raspberrypilearning/grandpa-scarer/en/images/gpio.png

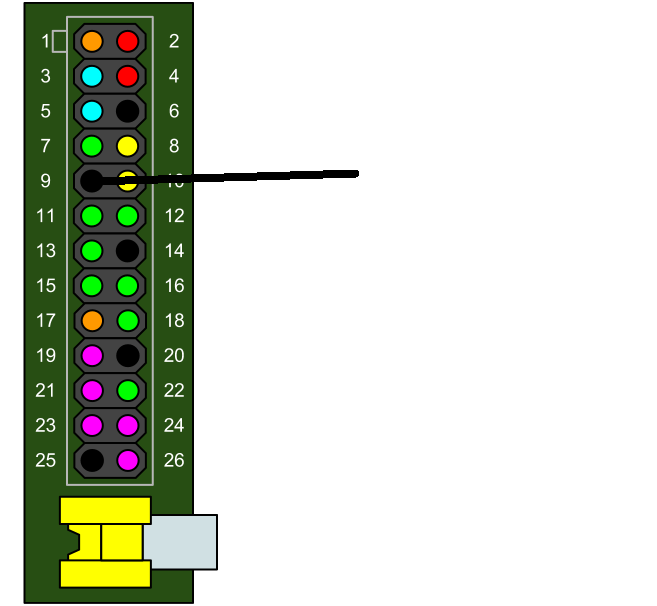
en/images/gpio.png
